matiassambrizzi/circuitos2_proyecto/FuenteConmutada/FUENTE DE ALIMENTACION FLYBACK - ejemplo de disenio.pdf

FUENTE DE ALIMENTACIÓN FLYBACK Ejemplo de diseño

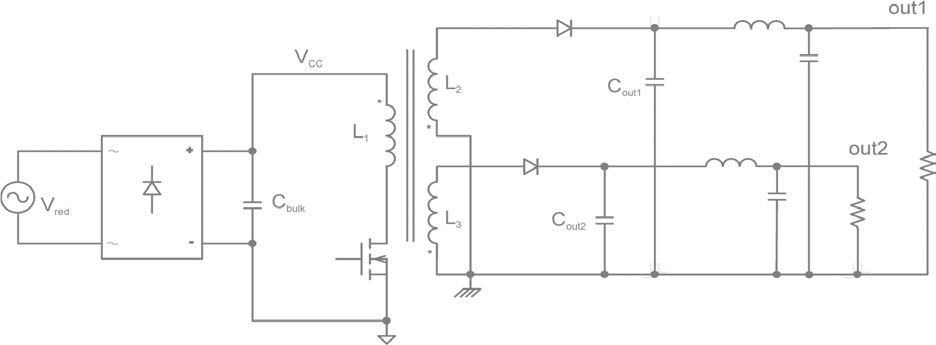
[picture p57: figure]

Datos
Operación: Modo de Conducción Discontinuo Frecuencia de conmutación 100KHz VCCMIN = 150V
Output1: | 12V±1.2V, Rizado 120mV, 2A
Output2: | 5V±0.5V, Rizado 50mV, 4A
VRED: | 220Vrms±10% de variación, 50Hz
THOLD-UP: | Entre 10ms y 15ms
| Desarrollo
Análisis preliminar
Del análisis de funcionamiento de un convertidor Flyback en el modo discontinuo, como se ha planteado para el circuito del enunciado, se observa la situación más crítica cuando se alcanza la potencia máxima, en que se tiene la tensión de alimentación VCC mínima y el regulador es llevado a operar al borde del modo continuo. En este caso son válidas las siguientes ecuaciones:

# II1MMMMMM = 2 PPSS SSSSSS VVCCCC CC DDMMMMMM

que da la corriente máxima que alcanzará el circuito primario durante la conducción de la llave (transistor MOSFET) en cada ciclo, lo que condicionará a ésta y al diseño del inductor L1 (cobre y núcleo). Y también

# LL1MMMMMM = VVCCCC CC DDMMMM II1MMMMMM ff

que da el valor máximo de inductancia del primario para asegurar el funcionamiento en modo discontinuo (un valor menor podría hacer que en alguna condición de carga y/o condición de la red de 220V el convertidor entrara en modo continuo).
Utilizando estas ecuaciones se calculan los valores preliminares máximos de L1 e I1.

# II1MMMMMM = 2 PPMMMMMM VVCCCC CC DDMMMMMM

= 2 . 36,4WW
150VV . 0,5

≅ 1AA

Se ha considerado un valor D = 0,5 como máximo dado que así se limita el tiempo de conducción de la llave al 50% en la situación límite planteada (justo entrando al modo continuo con mínima tensión de entrada y máxima carga).
El valor máximo para la inductancia L1 será entonces:

# L1MAX = VCCMIN DMAX

# I1Max f = 150VV . 0,5 1AA . 100KKKKKK = 750μμ

La especificación VCCMIN=150V ya tiene en cuenta el margen de seguridad necesario para que en un amplio rango de tensiones de entrada (de la red de 220V) el convertidor no entre en modo continuo. Incluso este valor de VCC es inferior al que se tomaría de la otra especificación del rango de tensiones de entrada dado por 220Veficaces−10%, asumiendo que el capacitor de filtro es suficientemente grande para que el rizado (ripple) sea acotado de manera de obtener este VCCMIN=150V operando el regulador con su máxima carga, aunque esto habrá que reverlo luego al calcular el THOLD-UP. Con esta aclaración se asume como valor para L1 el ya calculado, o sea L1 = 750µH.
Los valores de las inductancias del secundario estarán vinculados con L1 a través de la siguiente ecuación (dado su número de espiras N1 que se calculará más adelante para el inductor primario):

# NN12 = (VV12+ VVDD) (1− MMMMMM) 1

# (VVCCCC CCCC − VVLLLL LLLL) . MMMMMM

# y NN5 = (VV5+ VVDD) (1− MMMMMM) 1 (VVCCCC CCCC − VVLLLL LLLL) . MMMMMM

respectivamente para los devanados de 12V y 5V.
Estas ecuaciones suponen las mismas consideraciones de diseño que las de L1MAX e I1MAX, o sea justo entrando al modo continuo con mínima tensión de entrada y máxima carga. Resulta:

# NN12 = (12VV + 1VV) (1 − 0,5) NN1 (150VV − 2VV) . 0,5 = NN1

11,4

≅

NN1
12

y

# NN5 = (5VV + 1VV) (1 − 0,5) NN1 (150VV − 2VV) . 0,5 = NN1

24,7

≅

NN1
25

Aplicando ahora la relación entre dos inductancias que comparten el mismo núcleo (asumiendo concatenación completa del flujo magnético) se tiene:

# LL12 = LL1

NN12
NN1

2

= 750μμ 1
12
| 2
= 5,2μμ

y

# LL5 = LL1

NN5
NN1

2

= 750μμ 1
25
| 2
= 1,2μμ

Simulación 1
A fin de comprobar estos valores preliminares se realiza una simulación considerando componentes ideales, excepto las llaves, que estarán representadas por los modelos de transistor y diodo indicados en el siguiente esquema:

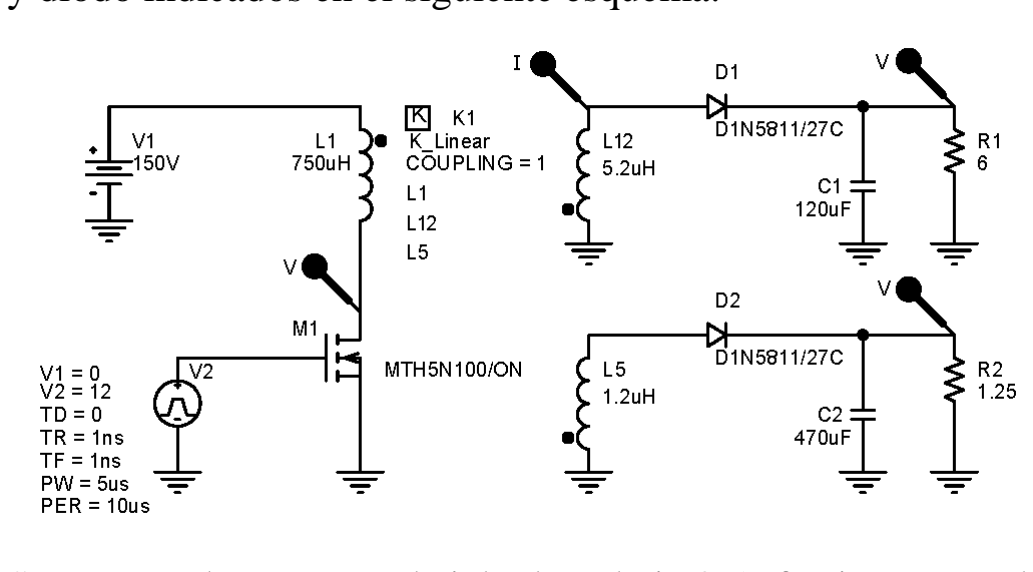
[picture p58: figure]

Se comprueba que con el ciclo de trabajo 0,5 efectivamente el conversor se encuentra operando al borde del modo continuo, lo que se evidencia en la forma de onda de la tensión en “Drain” de M1 y en la forma de onda de la corriente en L12.
Con los valores de L1, L12, L5, R1, R2, C1 y C2 empleados se logra cumplir con el rizado máximo en las tensiones de salida y las corrientes máximas correspondientes, según los datos, como puede apreciarse en las siguientes formas de onda medidas:

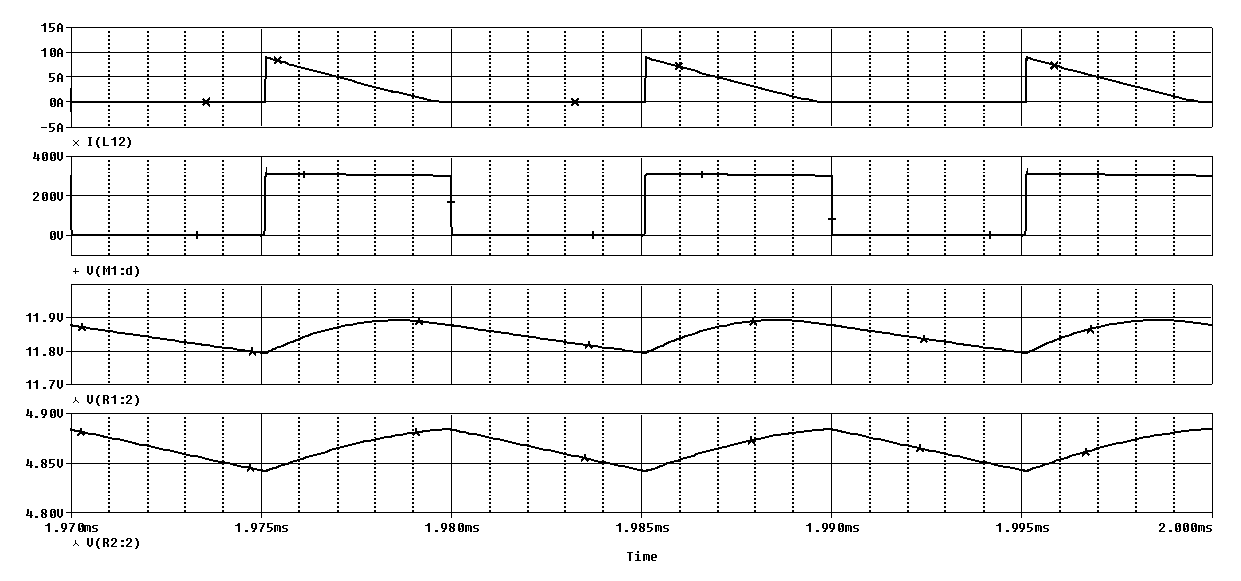
[picture p59: figure]

Diseño del transformador
En realidad no se trata de un transformador sino de tres inductores acoplados por un único núcleo.
Elección del material del núcleo
Consultando el catálogo de Ferroxcube se encuentra que la recomendación para convertidores tipo Flyback, respecto del material del núcleo, es 3C92, que permite operar con frecuencias de hasta 200KHz con altos niveles de saturación en un tamaño relativamente pequeño. Sin embargo consultando las hojas de datos se ve que este tipo no se fabrica con diferentes calibres de entrehierro, por lo que la elección del material del núcleo recae en la siguiente recomendación del fabricante, o sea el tipo 3F3.
Y para operar con potencias entre 20W y 50W a 100KHz se recomienda el formato de núcleo E25. (Ver página 29 del catálogo de Ferroxcube adjunto).

Determinación del tamaño del núcleo
Se impone el valor aceptado de la pérdidas en el núcleo en PV=10²

kW/m³
, con lo que se
determina para el material 3F3 operando a 100KHz, según el gráfico del fabricante, una inducción magnética BPICO=120mT

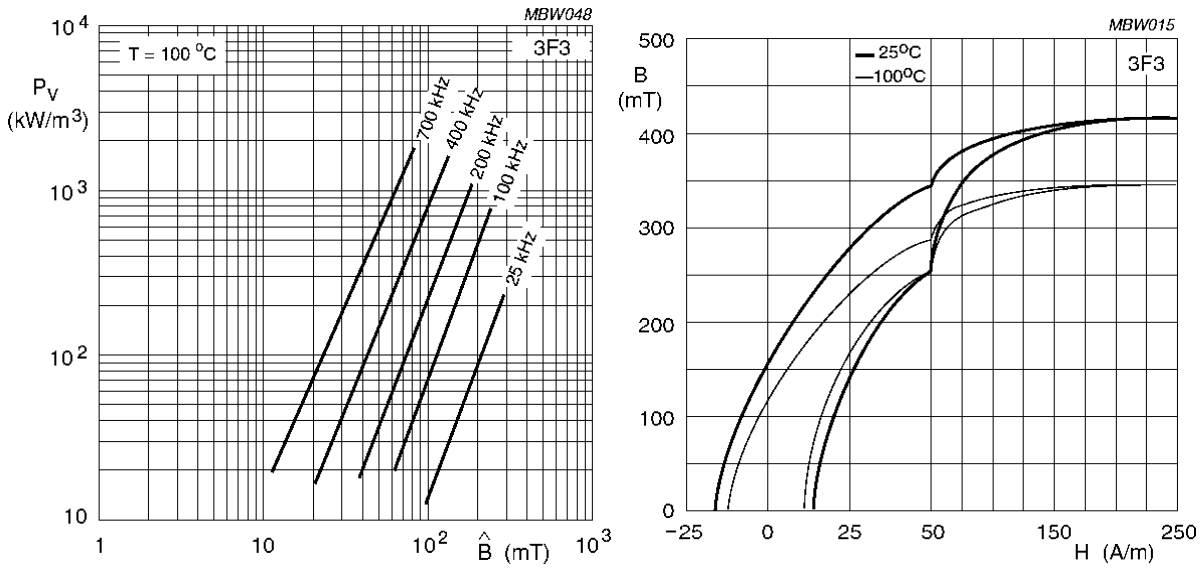
[picture p60: figure]

Debido al funcionamiento en modo discontinuo el valor medio de la inducción magnética en el núcleo será aproximadamente igual al valor pico, por lo que se alcanzará en el núcleo una inducción magnética igual a dos veces el valor BPICO, o sea que será: BMAX=2BPICO=240mT. Vemos en la gráfica suministrada por el fabricante que para el material seleccionado no se producirá saturación.
Se considerará el producto de las áreas efectivas de la ventana del bobinado y del camino magnético, a fin de dimensionar el núcleo.

# P = AVV V A N N = L IMMM 100 I E E

# BBMMMMMM KK JJ

Tomando el inductor primario, dado que es de los tres el que producirá toda la energía requerida para la conversión, se procede a estimar los valores asociados que se introducirán en la fórmula precedente.
Dada la forma de onda diente de sierra de la corriente se puede estimar su valor eficaz como:

# II EE EE = IIMMMMMMDDMMMMMM

3 = 1AA0,5
3 = 0,41AA

Reemplazando valores en PA se obtiene:

# PP = 750μμ . 1AA . 100 . 0,41AA 240mmmm . 0,2 . 300AA/cc 2 ≅ 0,22cc 4

En base a este valor elijo el tamaño E25/10/6 cuyos datos dimensionales son:

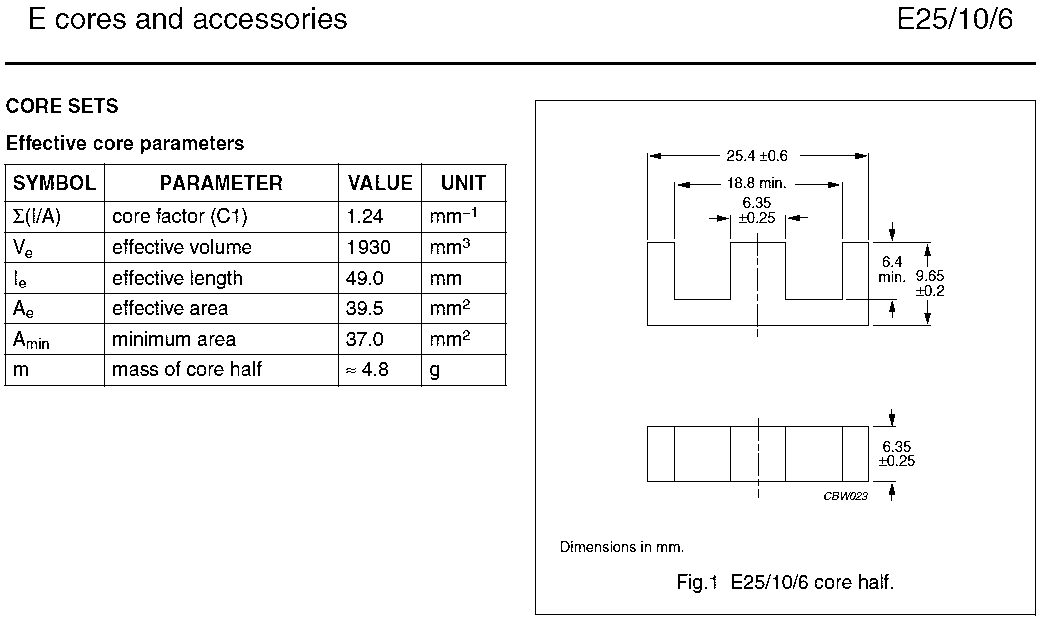
[picture p61: figure]

Calculando el área efectiva de la ventana como AVENTANA=(18,8mm−6,35).6,4mm=79,7mm² Y el producto de áreas efectivas como PA= AVENTANA.Ae=79,7mm²

.39,5mm²

=0,31cm⁴
Se compara con el valor requerido PA=0,22cm⁴ y se ve que el tamaño elegido es algo mayor, sin embargo se continuará con este tipo dado que permitirá un mejor acomodamiento de los tres devanados L1, L12 y L5 y sus respectivas aislaciones. Además el siguiente tamaño de núcleo escalando hacia abajo, E20, no llega a cumplir con el PA requerido y tampoco es recomendado por el fabricante para potencias mayores a 20W.
El entrehierro se determina valiéndose del ábaco facilitado por el fabricante.
Previamente al cálculo del entrehierro por medio del ábaco se calcula el valor I²
L requerido
como entrada al mismo mediante I²

L=1A²

.0,75H=0,75A²

H=0,75.10⁻³

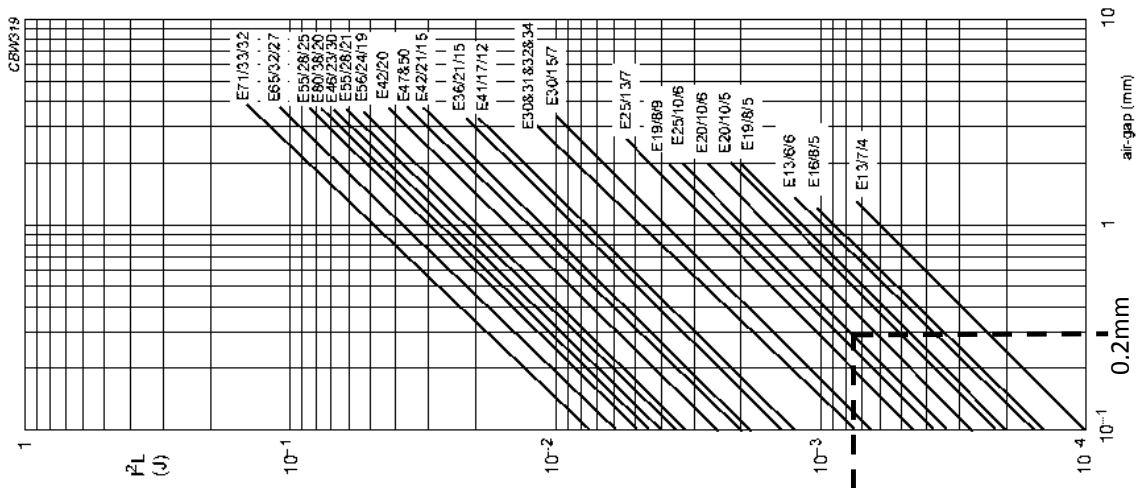
[picture p62: figure]

Resulta así un entrehierro de 0,2mm Determinación del número de espiras

0,75.10⁻³

J

Utilizando la tabla del fabricante Ferroxcube para el núcleo E25/10/6-3F3, introduciendo el dato obtenido en el párrafo anterior se podrá obtener el valor AL que permitirá calcular en número de espiras necesarios para realizar el inductor primario.

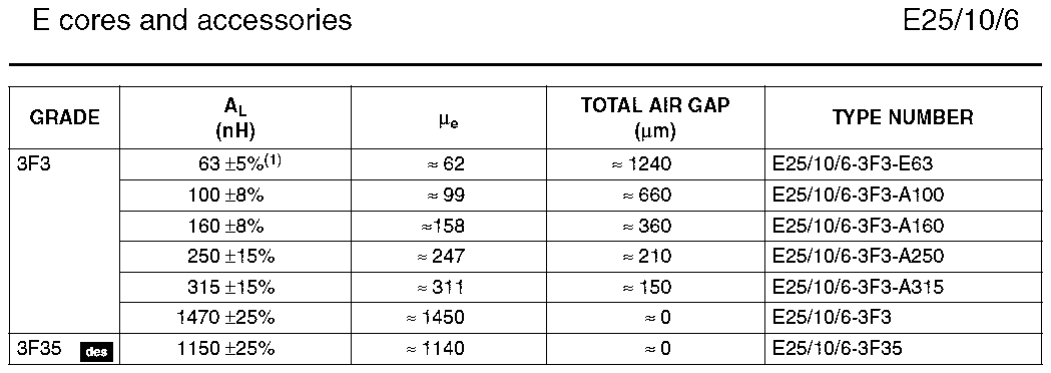
[picture p63: figure]

Resulta la elección apropiada el tipo número E25/10/6-3F3-250, que posee AL=250nH Con este valor se puede finalmente calcular el número de espiras mediante:

# NN1 = LL1

# AA = 750uu 0,25μμ = 55 eeeeeeeeeeeeee

Y según se había calculado anteriormente la relación de espiras entre los bobinados secundarios y primario, resulta el número de espiras de los bobinados secundarios:
NN12 = 1

12 = 55

# 12 = 4,58 y NN5 = 1 25 = 55

25 = 2,2

Por razones constructivas se escalará hacia abajo el número de espiras de todos los bobinados, llevándolos a N5=2e, N12=4e y N1=50e, con lo cual hay que rectificar todos los cálculos preliminares y verificar que se siga cumpliendo que el límite entre el modo discontinuo y continuo continua lográndose con un DMAX igual o levemente menor a 0,5 y que no se exceda los valores de B que saturarían el núcleo, así como que se mantengan acotadas las pérdidas por histéresis en el mismo.
El reducir el número de espiras llevará a valores de inductancia menores a los calculados, lo que es aceptable dado que los mismos correspondían a los máximos dados por la condición de operación en la situación extrema con VCCMIN=150V, I12=2A, I5=4A y DMAX=0,5.
Este proceso iterativo no se realizará en el presente trabajo pues lo llevaría a tener una gran extensión.

Comprobación de las condiciones de funcionamiento del núcleo
Utilizando los valores preliminares ya calculados se tendrá para la amplitud del flujo la siguiente situación:

# BBMMMMMM = LL1II1MMMMMM

| AAee NN1 = 750μμ . 1AA 39,5cc 2 . 55 = 345mmmm

Este valor es un 40% mayor que el adoptado en los cálculos previos. Resulta estar por debajo de la saturación del núcleo si se lo opera a 25ºC y ya entrando en saturación si la temperatura llega a los 100ºC, como se desprende de la observación de la curva B-H para el tipo de material 3F3 de Ferroxcube presentada en una sección anterior.
Las pérdidas por histéresis en el núcleo se calculan así:

# P N N = PV Ve

Tomando valores de la gráfica “pérdidas en el núcleo <−> Bpico” para el material 3F3 que se presentó en una sección previa, utilizando el dato BMAX calculado en el párrafo inmediato anterior, obteniendo BPICO=BMAX/2=345mT/2≈170mT (a 100ºC y 100KHz) y tomando de la tabla de dimensionamiento del tipo E25/10/6 el valor Ve, se tiene:

# P N N = PV Ve = 400

mm

# cc 3 1,93cc 3 ≅ 0,8WW

Se ve que las pérdidas en el núcleo resultarían aceptables, sin embargo la situación de operar cerca del límite de saturación obliga a replantear los cálculos, encaminándolos hacia un tipo de material que pueda operar con una mayor inducción magnética, o bien alterar la selección del tamaño del entrehierro para aumentar la reluctancia del circuito magnético a fin de reducir la inducción magnética máxima alcanzada en el núcleo, lo que llevará a aumentar el número de espiras para mantener los valores de inductancia máximos impuesto por los primeros cálculos.

Cálculo del devanado de cobre del inductor primario L1
Se utilizará un valor de densidad de corriente mayor al empleado en la determinación del núcleo.
Área de conductor = I1EFICAZ ÷ J ≈ 0,41A ÷ 500A/cm² = 0,082mm²
Esto lleva a un conductor de diámetro = 0,32mm
O bien dos conductores en paralelo de diámetro = 2 . (0,041mm2 ÷ 3,1416)

½ = 0,23mm
Para el bobinado del inductor primario se recomienda la utilización de alambre tipo Litz a fin de reducir o eliminar el efecto pelicular, o también trenzar dos alambres tipo AWG30 (de diámetro 0,26mm) ya que el efecto pelicular a 100KHz es de 0,2mm (muy semejante al diámetro de este alambre) y no resulta afectada la relación Rac/Rdc que es unitaria para este tipo de alambre. El empleo de 2 alambres AWG30 en paralelo llevaría a un incremento del área originalmente calculada de un 30% teniendo quizás problemas para que todo el devanado quepa en el espacio correspondiente de la ventana, lo que también puede analizarse más adelante. Claro que como se vio al elegir el tamaño del núcleo, éste excede el PA requerido, por lo que seguramente quedará bien alojado el bobinado primario usando dos AWG30 trenzados.

Cálculo del devanado de cobre del inductor secundario L12
Área de conductor = I12EFICAZ ÷ J ≈ 12A . (0,5÷3)½ ÷ 500A/cm² = 0,98mm²
Esto lleva a un conductor de diámetro = 1,12mm y que para corriente continua correspondería un AWG16, sin embargo a 100KHz el efecto pelicular reduciría notablemente el área efectiva, por lo que se propone utilizar varios alambres en paralelo del tipo AWG26 de 0,4052mm de diámetro, ya que su relación Rca/Rcc es unitaria, mediante la siguiente ecuación:
Nπ

# ∅AGW26

2

2
= 0,98mm2

Resulta N = 7,6 ≈ 8
Para el bobinado del inductor secundario L12 se recomienda la utilización de 8 alambres AWG26 trenzados. El empleo de 8 alambres AWG26 en paralelo trenzados llevaría a un incremento del área originalmente calculada de un 5% no presentando problema alguno en el alojamiento del devanado en el espacio correspondiente de la ventana dado que como se vio al elegir el tamaño del núcleo, éste excede el PA requerido, por lo que seguramente quedará bien alojado el bobinado secundario L12 usando 8 AWG26 trenzados.

Cálculo del devanado de cobre del inductor secundario L5
Área de conductor = I12EFICAZ ÷ J ≈ 25A . (0,5÷3)½ ÷ 500A/cm² = 2,04mm²
Se propone utilizar varios alambres en paralelo del tipo AWG26 de 0,4052mm de diámetro, ya que su relación Rca/Rcc es unitaria, mediante la siguiente ecuación:
Nπ

# ∅AGW26

2

2
= 2,04mm2

Resulta N = 15,82 ≈ 16
Para el bobinado del inductor secundario L5 se recomienda la utilización de 2 alambres multifilares conformados por 8 alambres AWG26 trenzados cada uno. El empleo de 16 alambres AWG26 en paralelo llevaría a un incremento del área originalmente calculada de un 1% no presentando problema alguno en el alojamiento del devanado en el espacio correspondiente de la ventana dado que como se vio al elegir el tamaño del núcleo, éste excede el PA requerido, por lo que seguramente quedará bien alojado el bobinado secundario L5 usando 2 paquetes multifilares de 8 alambres AWG26 trenzados.

Pérdidas en los conductores
La resistencia de cada bobinado se calcula mediante la siguiente ecuación:

# RR = KK RR = KK ρρCC

# llMM MM NN EE EE

# AA AA

Siendo:
K = Factor de relación corriente alterna-corriente continua
ρCU = Resistividad del cobre = 2,3.10⁻⁶ Ω.cm a 100ºC
lMEDIA = Longitud media del alambre en cada espira para el tipo de núcleo utilizado AALAMBRE = Área de la sección del alambre seleccionado

Se calcula para cada bobinado, resultando: R1 = 0,6Ω
R12 = 4,4mΩ
R5 = 1,1mΩ
La potencia disipada en el cobre es:
PCU = I1EFICAZ2 . R1 + I12EFICAZ2 . R12 + I5EFICAZ2 . R5 = 0,1W + 0,105W + 0,115W = 0,32W

Tabla de alambres

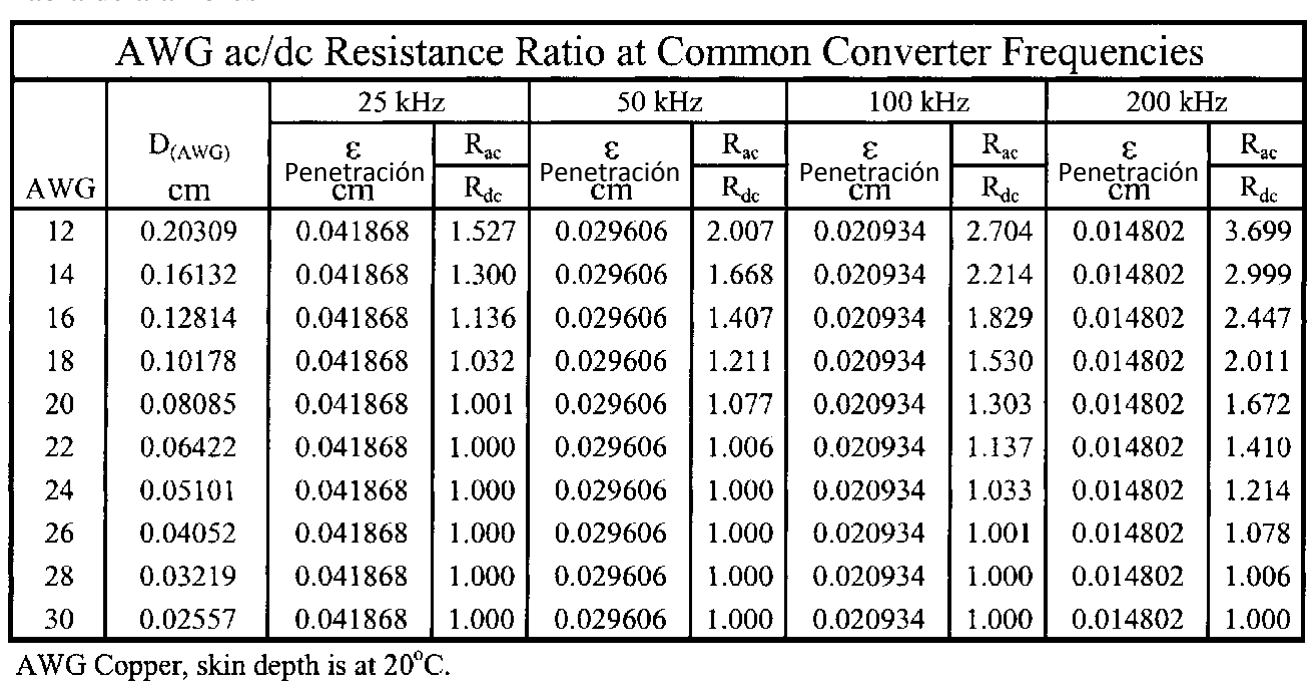
[picture p64: figure]

Cálculo del capacitor de filtro considerando el THOLD-UP
Se utilizará un método simplificado, considerando que la energía que entrega el capacitor se descarga sobre el primario del regulador asumiendo que éste le demanda la máxima corriente desde la interrupción de la tensión de red hasta que VCC alcanza 150V.
Si la eficiencia fuese 100% entonces la corriente media demandada por el regulador operando
con VCC=150V sería IMEDIA_ENTRADA=PENTRADA/VCCMIN=PSALIDA/VCCMIN , lo que da:
I =36,4W/150V=0,24A
Asumiendo que la tensión de red se encuentra en un mínimo de 200VEFICACES tendremos a la salida del rectificador una tensión pico de 280V.
Si el capacitor se descarga a una corriente constante de 0,24A desde 280V hasta 150V, en un tiempo TH de 15ms (dato especificado), será.

# CC = II . HH

# ∆VV = 0,24AA . 15mm 280VV − 150VV = 28uuuu

Con una tensión de trabajo especificada de 400V

Penetración | Penetración | Penetración | Penetración

Dimensionamiento y selección de los capacitores para las salidas de 12V y 5V

Los valores de estos capacitores se encontraron por simulación y resultaron ser de 120µF para la salida de 12V y de 470µF para la salida de 5V, alcanzando un rizado de aproximadamente 100mVpp y 40mVpp respectivamente, por debajo de la cota máxima impuesto en los datos del problema. No se ha efectuado el cálculo de los filtros de salida, los cuales reducirán aún más el rizado, permitiendo a su vez emplear valores de capacitores de salida algo menores a los recién dimensionados.
En dicha simulación se consideraron componentes ideales, excepto las llaves, por lo que se podría refinar aún más los cálculos por este método simulando con modelos más aproximados a los reales, por ejemplo incluyendo las resistencias serie en los capacitores e inductancias, más inductancias de dispersión producto de un acoplamiento K<1 entre los inductores y efectos del layout en la implementación física.
Los capacitores mencionados de 120µF y 470µF deberían ser del tipo rotulado ESR o LOWZ y especificarse para tensiones de trabajo de 16V y 10V respectivamente. Generalmente el comportamiento de dos o más capacitores en paralelo es mejor respecto de la resistencia equivalente serie que uno solo, a la vez que resuelve el acomodamiento espacial y volumétrico en la implementación física.

Conclusiones
Como se mencionó durante el desarrollo del trabajo, en material elegido para el núcleo cumple perfectamente con la operación normal del regulador, sin embargo a muy alta temperatura, digamos 100ºC, el núcleo podría saturar, lo cual requiere una revisión completa del cálculo para refinarlo y acomodarlo a las características de este material o eventualmente utilizar otro tipo de material con mayor nivel de saturación admitida de inducción magnética B o bien intentar con otros valores de entrehierro.
Queda pendiente estudiar el comportamiento del regulador para diferentes condiciones de tensión de entrada y carga, verificando el acotamiento de las tensiones de salida entre el ±10% especificado.
Restaría incluir un controlador que ajuste automáticamente del ciclo de trabajo D (con máximo de 0,5) para estabilizar las tensiones de salida ante variaciones de la carga y/o la tensión de red de 220V.
Este regulador estaría sensando una u otra de las tensiones de salida, o un promedio de ambas. Esta elección dependerá del uso del convertidor y el comportamiento de la carga.
Igualmente para lograr un buen seguimiento de ambas tensiones, especialmente cuando se muestrea solo una de ellas, se debe tener especial cuidado en la construcción de los devanados secundarios de modo de concatenar eficazmente el flujo magnético entre sí y con respecto al devanado primario.
Dado que el modo de funcionamiento es el discontinuo, resultará mucho más simple la compensación del lazo de control ya que será de un solo polo, en lugar de dos como ocurriría si se operase en modo continuo.
Ingeniero José Alberto Bertuccio
