matiassambrizzi/circuitos2_proyecto/simulaciones/circuitoPolarizacionA25.png

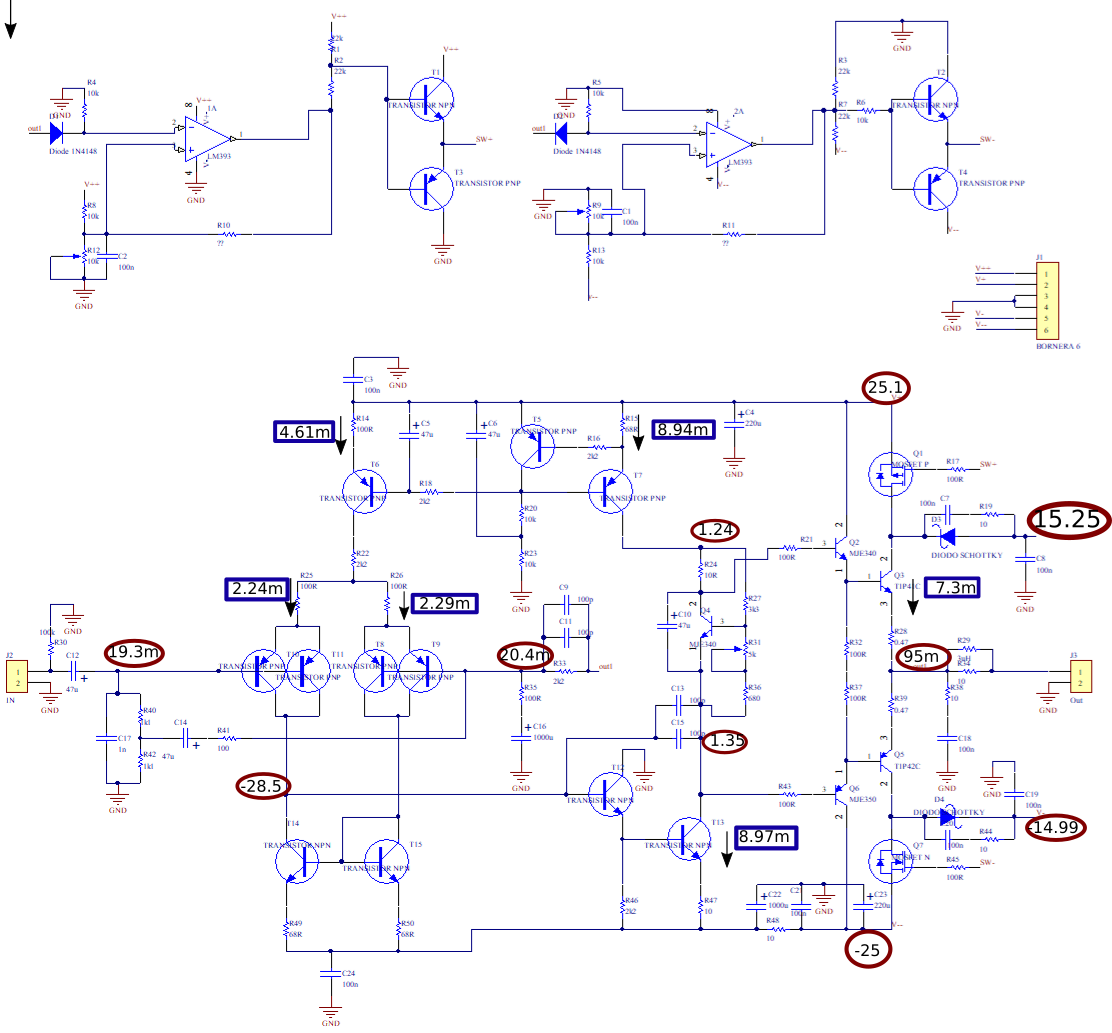
simulaciones/circuitoPolarizacionA25.png
