matiassambrizzi/circuitos2_proyecto/Circuitos II-20181207T191743Z-001/Circuitos II/PCB/botlayer.pdf

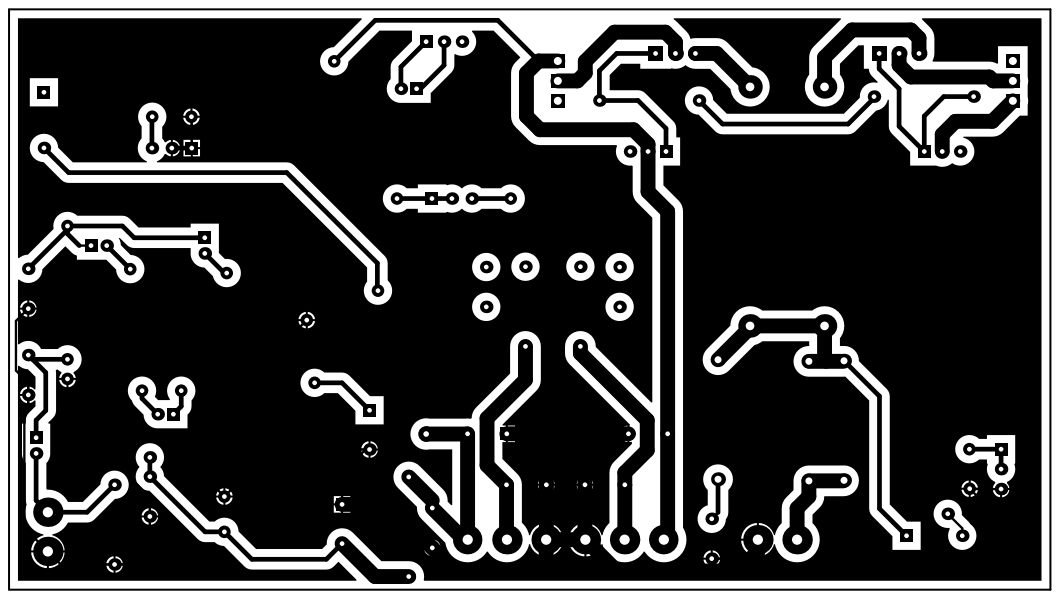
[picture p110: page 1]
