matiassambrizzi/circuitos2_proyecto/Circuitos II-20181207T191743Z-001/Circuitos II/PCB/toplayer.pdf

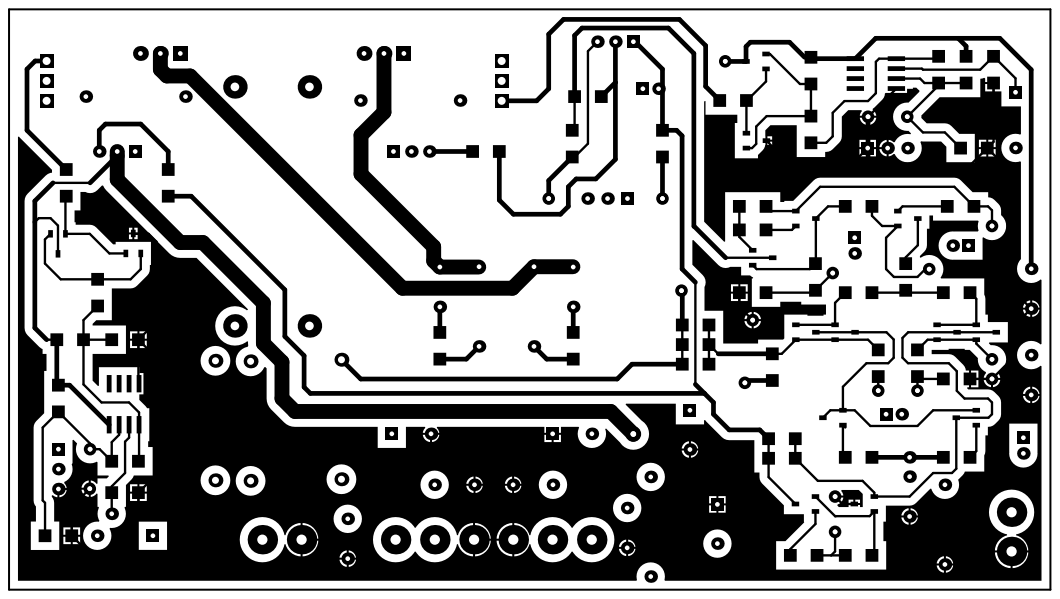
[picture p111: page 1]
