matiassambrizzi/circuitos2_proyecto/FuenteConmutada/simusFuentes.asc

C1: cap; 220µ
C2: cap; 680µ
C3: cap; 220µ
D1: schottky; MBR745
D2: schottky; MBR745
L1: ind; 150µ
L2: ind; 150µ
M1: nmos; IRFB4410Z
M2: nmos; IRFB4410Z
R1: res; 100
R2: res; 100
V1: voltage; PULSE(0 30 1p 1p 1p 3u 6u)
V2: voltage; 30
V3: voltage; PULSE(0 30 1p 1p 1p 1.25u 2.5u)
V4: voltage; -30
Named nets: 0
.tran 100m
