matiassambrizzi/circuitos2_proyecto/simulaciones/douglasSape.asc

C1: cap; 47µ
C2: cap; 100n
C3: cap; 100p
C4: cap; 47µ
C5: cap; 47µ
C6: cap; 100n
C7: cap; 1000µ
C8: cap; 47µ
D1: schottky; 1N5819
D2: schottky; 1N5819
D3: diode; RFU01SM4S
M1: nmos; BSB012N03LX3
M2: pmos; IRF9640
Q1: pnp; MPSA56
Q2: pnp; MPSA56
Q3: npn; MPSA06
Q4: npn; MPSA06
Q5: pnp; MPSA56
Q6: pnp; MPSA56
Q7: pnp; MPSA56
Q8: npn; MPSA06
Q9: npn; MPSA06
Q10: pnp; MPSA56
Q11: pnp; MPSA56
Q12: npn; MJE340
Q13: npn; MJE340
Q14: npn; TIP31C
Q15: pnp; TIP32C
Q16: pnp; MJE350
Q17: npn; MJE340
Q19: npn; MPSA06
R1: res; 50
R2: res; 100
R3: res; 100
R4: res; 68
R5: res; 68
R6: res; 1k1
R7: res; 1k1
R8: res; 100
R9: res; 10k
R10: res; 10
R11: res; 2.2k
R12: res; 2k2
R13: res; 10k
R14: res; 2.2k
R15: res; 68
R16: res; 2k
R17: res; 2.2k
R18: res; 2k2
R19: res; 100
R20: res; 1k
R21: res; 3k3
R22: res; 100
R23: res; 100
R24: res; .47
R25: res; .47
R26: res; 8
R27: res; 500
R28: res; 100
R29: res; 50
R30: res; 1k
R123: res; 100
U1: opamp2; LM339
U2: opamp2; LM339
V1: voltage; 30
V2: voltage; 30
V3: voltage; SINE(0 .9 {freq})
V4: voltage; 10
V5: voltage; 30
V7: voltage; 15
V8: voltage; 15
V9: voltage; -11
V10: voltage; 30
Named nets: 0, entrada_pos, vout
.lib Includes/standard.bjt
.tran 0 2m 1m
.inc Includes/standard.dio
;four {freq} V(vout)
.param freq=1k
Input pairs before and after constant-gm
degeneration, showing how to double stage current while
keeping transconductance constant; distortion is reduced
by about ten times.
Not all benefit when we add emitter-
degeneration resistors. The extra resistances will
generate Johnson noise, increasing the total noise from
the input stage.
Etapa de entrada
;OPTIONS plotwinsize=0
;OPTIONS numdgt=12
;OPTIONS temp=25
.lib Includes/LM339.sub
