matiassambrizzi/circuitos2_proyecto/simulaciones/Intento etapa de entrada.asc

C1: cap; 100p
C2: cap; 1000µ
D1: schottky; MBRS340
D2: schottky; MBRS340
Q1: npn; BC547B
Q2: npn; QBD135
Q3: npn; Qtip41c
Q4: pnp; Qtip42c
Q5: pnp; Qtip42c
Q6: npn; Qtip41c
Q9: npn; QBD135
Q10: npn; QBD135
Q11: pnp; QBD136
Q16: npn; BC547B
Q17: npn; BC547B
Q18: pnp; BC557B
Q19: pnp; BC557B
Q20: npn; BC547B
Q21: npn; BC547B
Q22: pnp; BC557B
Q23: pnp; BC557B
Q24: npn; BC547B
R1: res; 60
R2: res; 5k
R3: res; 1k6
R4: res; 3k
R5: res; 100
R6: res; 0.47
R7: res; 220
R8: res; 220
R9: res; 100
R10: res; 47k
R11: res; 100
R12: res; 1k
R13: res; 8
R14: res; 100
R20: res; 1k
R21: res; 2k2
R22: res; 0.47
R23: res; 100
R24: res; 300
R25: res; 500
U1: LT1716
U2: LT1716
V1: voltage; 30
V2: voltage; 30
V3: voltage; SINE(0 300m {freq})
V4: voltage; 15
V5: voltage; 15
V6: voltage; 13
V7: voltage; 13
V8: voltage; 11
V9: voltage; 30
V11: voltage; 30
V12: voltage; -11
Named nets: 0, -Vh, +Vh, in, realim, out, +Vl, -Vl, +Vcomp, -Vcomp
Las Rs de emisor son bastante buenas, me reducen mucho la distorsion de la etapa
p.141 D-S
.tran 0 23m 20m 1u
.four {freq} V(out)
.lib Includes/BC548B.LIB
.lib Includes/BC558B.LIB
.lib Includes/BD135.LIB
.inc Includes/BD136.lib
.lib Includes/TIP41.lib
;step param freq list 1k 20
.param freq=1k
.lib Includes/TIP42C.lib
.inc LTC.lib
