matiassambrizzi/circuitos2_proyecto/simulaciones/Amplificadores/douglasSape.asc

C1: cap; 47µ
C2: cap; 100n
C3: cap; 50p
C4: cap; 47µ
C5: cap; 47µ
C6: cap; 100n
C7: cap; 1000µ
C8: cap; 47µ
C9: cap; 47µ
C10: cap; 10n
C11: cap; 10n
C12: cap; 1n
C13: cap; 220p
C14: cap; 100n
C15: cap; 1000µ
C16: cap; 100n
D1: schottky; MBR20100CT
D2: schottky; DI_MBRM3100
D4: diode; DI_1N4937
D5: diode; DI_1N4937
L1: ind; 3µ
M1: nmos; IRF7303
M2: pmos; IRF7205
Q1: pnp; MPSA56
Q2: pnp; MPSA56
Q3: npn; MPSA06
Q4: npn; MPSA06
Q5: pnp; MPSA56
Q6: pnp; MPSA56
Q7: pnp; MPSA56
Q8: npn; MPSA06
Q9: npn; MPSA06
Q10: pnp; MPSA56
Q11: pnp; MPSA56
Q12: npn; MJE340
Q13: npn; MJE340
Q14: npn; Qtip41c
Q15: pnp; Qtip42c
Q16: pnp; MJE350
Q17: npn; MPSA06
Q18: pnp; MPSA56
Q19: npn; MPSA06
Q20: pnp; MPSA56
R1: res; 50
R2: res; 100
R3: res; 100
R4: res; 68
R5: res; 68
R6: res; 1k1
R7: res; 1k1
R8: res; 100
R9: res; 10k
R10: res; 10
R11: res; 2.2k
R12: res; 2k2
R13: res; 10k
R14: res; 2.2k
R15: res; 68
R16: res; 1.680k
R17: res; 2.2k
R18: res; 2k2
R19: res; 100
R20: res; 22k
R21: res; 3k3
R22: res; 100
R23: res; 100
R24: res; .47
R25: res; .47
R26: res; 8
R27: res; 10k
R28: res; 4.7k
R29: res; 22k
R30: res; 10
R31: res; 100
R32: res; 100
R33: res; 10
R34: res; 10k
R35: res; 22k
R36: res; 10k
R37: res; 4.7k
R38: res; 22k
R39: res; 1.1
R40: res; 1.1
R41: res; 10
R42: res; 10k
R43: res; 10
R44: res; 100
R45: res; 100
R46: res; 10k
R123: res; 100
U1: opamp2; LM339
U2: opamp2; LM339
V3: voltage; SINE(0 0 {freq}); AC 1
V6: voltage; 30
V11: voltage; -30
V12: voltage; 15
V13: voltage; -15
Named nets: 0, entrada_pos, vout, v++, v--, v-, v+, parlante
.lib ../Includes/standard.bjt
.tran 0 0.15m 0.05m
.inc ../Includes/standard.dio
.four {freq} V(parlante)
.param freq=20k
Input pairs before and after constant-gm
degeneration, showing how to double stage current while
keeping transconductance constant; distortion is reduced
by about ten times.
Not all benefit when we add emitter-
degeneration resistors. The extra resistances will
generate Johnson noise, increasing the total noise from
the input stage.
Etapa de entrada
;OPTIONS plotwinsize=0
;OPTIONS numdgt=12
;OPTIONS temp=25
.lib ../Includes/LM339.sub
.MODEL DI_1N4937 D  ( IS=830n RS=34.0m BV=600 IBV=5.00u
+ CJO=26.5p  M=0.333 N=2.46 TT=288n )
.lib ../Includes/TIP41C.lib
.lib ../Includes/TIP42C.lib
