matiassambrizzi/circuitos2_proyecto/Circuitos II-20181207T191743Z-001/Circuitos II/Simu/douglasSape.asc

100p: cap; 100
C1: cap; 47µ
C2: cap; 100n
C4: cap; 47µ
C5: cap; 47µ
C6: cap; 100n
C7: cap; 1000µ
C8: cap; 47µ
C12: cap; 1n
Q1: pnp; MPSA56
Q2: pnp; MPSA56
Q3: npn; MPSA06
Q4: npn; MPSA06
Q5: pnp; MPSA56
Q6: pnp; MPSA56
Q7: pnp; MPSA56
Q8: npn; MPSA06
Q9: npn; MPSA06
Q10: pnp; MPSA56
Q11: pnp; MPSA56
R2: res; 100
R3: res; 100
R4: res; 68
R5: res; 68
R6: res; 1k1
R7: res; 1k1
R8: res; 100
R9: res; 10k
R10: res; 10
R11: res; 2.2k
R12: res; 2k2
R13: res; 10k
R14: res; 2.2k
R15: res; 68
R17: res; 2.2k
R18: res; 2k2
R19: res; 100
R26: res; 50
R48: res; 100k
R123: res; 100
V1: voltage; SINE(0 500m 1k)
V6: voltage; 30
V11: voltage; -30
V12: voltage; 15
V13: voltage; -15
Named nets: 0, entrada_pos, v++, v--, v-, v+
.lib ../Includes/standard.bjt
.tran 0 10m 5m 10u
.inc ../Includes/standard.dio
;OPTIONS plotwinsize=0
;OPTIONS numdgt=12
;OPTIONS temp=25
.lib ../Includes/LM339.sub
.lib ../Includes/TIP41C.lib
.lib ../Includes/TIP42C.lib
